irfan-hossain/DAQ/DAQ/register.cpp

///////////////////////////////////////////////////////////////////////////////
//`File: configReg.h
// Desc: A file that contains all the functions to configure register for the
//       ADC and Timer1. See README.md for more information.
//
// Author: Irfan Hossain
///////////////////////////////////////////////////////////////////////////////
#include <Arduino.h>
#include "register.h"

static const uint16_t PRESCALER_INTERRUPT = 1249;

/////////////////////////////////////////////////////////
// module: configADMUX
//
// desc: Set registers relating to ADC input pin and 
// whether to left shift conversion.
//
// inputs: none
//
// outputs: none
//
// return: none
/////////////////////////////////////////////////////////
void configADMUX()
{
 // Set Register to all zeros, this means A0
 // will be used for input and the reference
 // voltage comes from AREF.
 ADMUX = 0x00;

 // Set bit 5 (ADLAR) to left shift conversion
 // result. This creats an 8-bit result in
 // ADCH.
 ADMUX |= (1 << ADLAR);
}

/////////////////////////////////////////////////////////
// module: configADCSRA
//
// desc: Configure register to turn ADC on, the autotrigger, 
// and set the ADC clock prescaler.
//
// inputs: none
//
// outputs: none
//
// return: none
/////////////////////////////////////////////////////////
void configADCSRA()
{
  // Turn ADC on.
  ADCSRA |= (1 << ADEN);

  // Enable auto trigger so Timer1 can trigger
  // the ADC.
  ADCSRA |= (1 << ADATE);

  // Set the ADC prescaler. PRESCALER = 8.
  ADCSRA &= ~(1 << ADPS2);
  ADCSRA |= (1 << ADPS1);
  ADCSRA |= (1 << ADPS0);
}

/////////////////////////////////////////////////////////
// module: configADCSRB
//
// desc: Configure Timer1 mode.
//
// inputs: none
//
// outputs: none
//
// return: none
/////////////////////////////////////////////////////////
void configADCSRB()
{
  // ACME is not used and should be set to zero.
  ADCSRB &= ~(1 << ACME);

  // Set Timer1 to Compare Match B
  ADCSRB |=  (1 << ADTS2);
  ADCSRB &= ~(1 << ADTS1);
  ADCSRB |=  (1 << ADTS0);
}

/////////////////////////////////////////////////////////
// module: configTCCR1A
//
// desc: Has bits to set register of
// TOP register for Timer1.
//
// inputs: none
//
// outputs: none
//
// return: none
/////////////////////////////////////////////////////////
void configTCCR1A()
{
  // Sets normal operation and starts part 1 to select
  // ICR1 as the TOP register.
  TCCR1A = 0x00;
}

/////////////////////////////////////////////////////////
// module: configTCCR1B
//
// desc: Has bits to set register of
// TOP register for Timer1 and set the
// Timer1 prescaler.
//
// inputs: none
//
// outputs: none
//
// return: none
/////////////////////////////////////////////////////////
void configTCCR1B()
{
  // Set register equal to 0x00 at the beginning and then
  // set WGM13 and WGM12. This is part 2 to select ICR1
  // as the TOP register.
  TCCR1B = 0x00;
  TCCR1B |= (1 << WGM13);
  TCCR1B |= (1 << WGM12);

  // Set CS12, CS11, and CS10 to 010 to set the Timer1
  // prescaler to 8. PRESCALER = 8;
  TCCR1B &= ~(1 << CS12);
  TCCR1B |= (1 << CS11);
  TCCR1B &= ~(1 << CS10);
}

/////////////////////////////////////////////////////////
// module: configICR1
//
// desc: Set TOP value.
//
// inputs: none
//
// outputs: none
//
// return: none
/////////////////////////////////////////////////////////
void configICR1()
{
  // With a PRESCALER of 8 and TOP value of 1249, the interrupt
  // frequency is 16 KHz.
  ICR1 = PRESCALER_INTERRUPT;
}

/////////////////////////////////////////////////////////
// module: enableInterrupts
//
// desc: Enable Timer1, ADC, and Pin 2
// interrupts.
//
// inputs: none
//
// outputs: none
//
// return: none
/////////////////////////////////////////////////////////
void enableInterrupts()
{

  // Enable Timer1 CMB.
  TIMSK1 |= (1 << OCIE1B);
  TCNT1   = 0;

  // ADC interrupt setup.
  ADCSRA |= (1 << ADEN); // Enable ADC
  ADCSRA |= (1 << ADIE); // Enable ADC
  ADCSRA |= (1 << ADSC); // Start first conversion
}

/////////////////////////////////////////////////////////
// module: disableInterrupts
//
// desc: Disable Timer1, ADC, and Pin 2 interrupts.
//
// inputs: none
//
// outputs: none
//
// return: none
/////////////////////////////////////////////////////////
void disableInterrupts()
{

  // Disable Timer1 CMB.
  TIMSK1 |= ~(1 << OCIE1B);

  // ADC interrupt setup.
  ADCSRA |= ~(1 << ADEN); // Disable ADC
  ADCSRA |= ~(1 << ADIE); // Disable ADC
  ADCSRA |= ~(1 << ADSC); // Disable first conversion
}

/////////////////////////////////////////////////////////
// module: setupRegisters
//
// desc: Function to wrap all the setup functions
// to be called in setup.
//
// inputs: none
//
// outputs: none
//
// return: none
/////////////////////////////////////////////////////////
void setupRegisters()
{
  // disable interrupts
  cli();

  // Configure registers
  configADMUX();
  configADCSRA();
  configADCSRB();
  configTCCR1A();
  configTCCR1B();
  configICR1();

  // enable interrupts
  sei();
}
